master-NORG/JunoCTRL-1.3/JunoCTRL Photos/IMG_0353.JPG

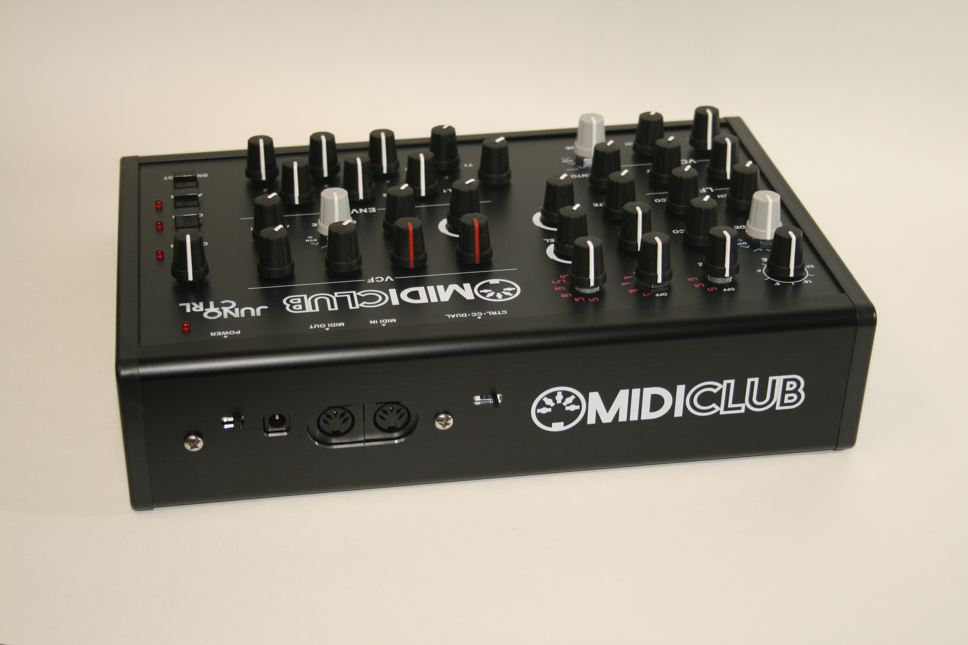
JunoCTRL Photos/IMG_0353.JPG
